likeablob/spin-maru/kicad/spin_maru.kicad_sch

## KiCad design kicad/spin_maru.kicad_sch (2025-04-28)

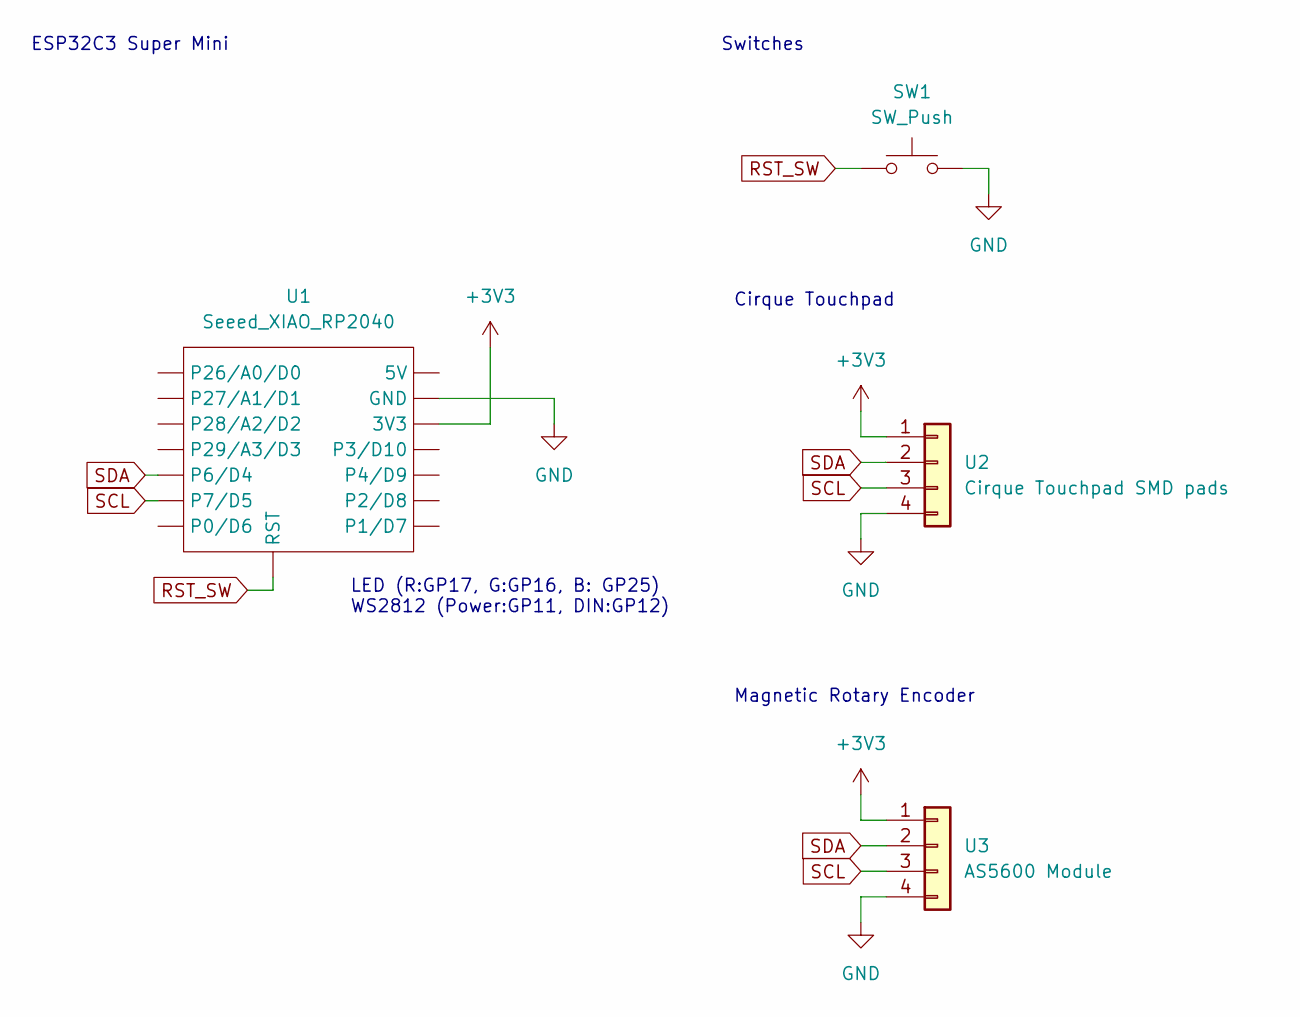
[picture p15: schematic spin_maru.kicad_sch]

Parts:
SW1: SW_Push
U1: Seeed_XIAO_RP2040
U2: Cirque Touchpad SMD pads
U3: AS5600 Module

Connections:
+3V3: U1., U2.1, U3.1
GND: SW1.2, U1., U2.4, U3.4
RST_SW: SW1.1, U1.
SCL: U1., U2.3, U3.3
SDA: U1., U2.2, U3.2

Notes on the sheet:
Magnetic Rotary Encoder
Cirque Touchpad
ESP32C3 Super Mini
LED (R:GP17, G:GP16, B: GP25) WS2812 (Power:GP11, DIN:GP12)
Switches
